Cocos44/Proiect-TSC/Images/ceas_exploded_view.png

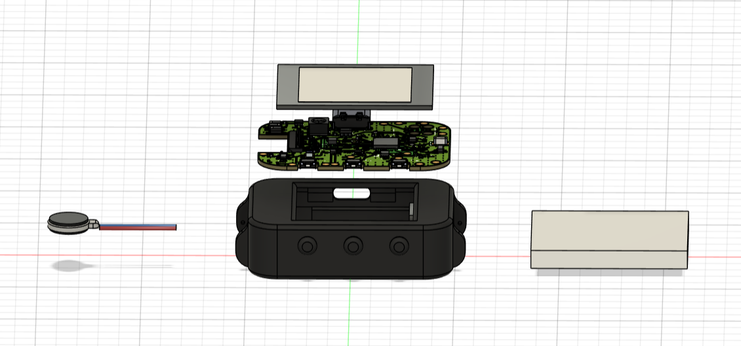
Images/ceas_exploded_view.png
