Cocos44/Proiect-TSC/Images/pcb_3D_fata.png

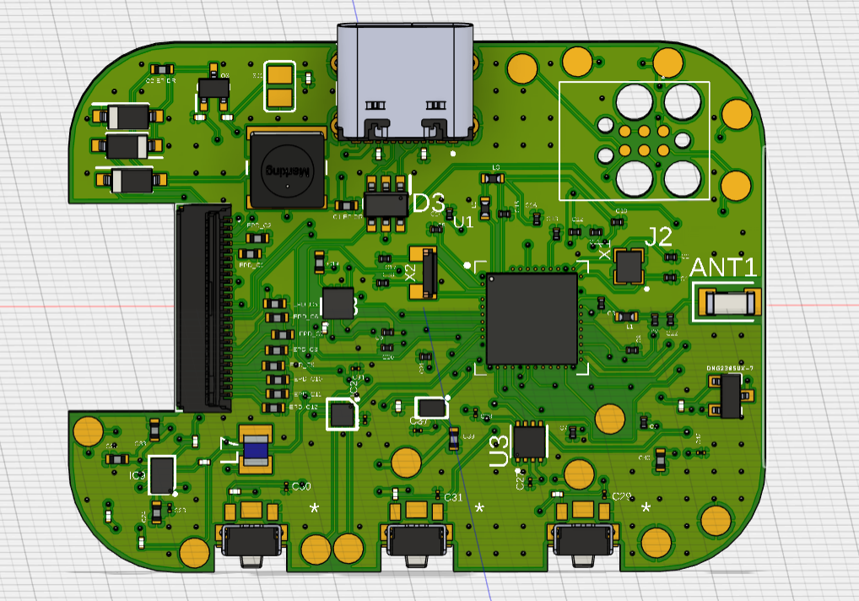
Images/pcb_3D_fata.png
